PaoloEstorm/Arpmini/Arpmini_Font.h

#include <stdint.h>
#include <Arduino.h>

const uint8_t ArpminiFont[][5] PROGMEM = {
  { 0x00, 0x00, 0x00, 0x00, 0x00 },  // 0x20 32
  { 0x00, 0x5c, 0x00, 0x00, 0x00 },  // 0x21 33 !
  { 0x10, 0x28, 0x44, 0x28, 0x10 },  // 0x22 34 " = empty shift icon
  { 0x28, 0x7c, 0x28, 0x7c, 0x28 },  // 0x23 35 #
  { 0x20, 0x60, 0xfe, 0x60, 0x20 },  // 0x24 36 $ = down arrow
  { 0x44, 0x20, 0x10, 0x08, 0x44 },  // 0x25 37 %
  { 0x40, 0x40, 0x7c, 0x04, 0x04 },  // 0x26 38 & = octave icon
  { 0x60, 0x60, 0x7c, 0x0c, 0x18 },  // 0x27 39 ' = music note icon
  { 0x6c, 0x44, 0x00, 0x44, 0x6c },  // 0x28 40 ( = empty selected box
  { 0x6c, 0x7c, 0x38, 0x7c, 0x6c },  // 0x29 41 ) = full selected box
  { 0x00, 0x10, 0x28, 0x10, 0x00 },  // 0x2A 42 * = small circle
  { 0x10, 0x10, 0x7c, 0x10, 0x10 },  // 0x2B 43 +
  { 0x74, 0x68, 0x60, 0x68, 0x74 },  // 0x2C 44 , = drum icon
  { 0x10, 0x10, 0x10, 0x10, 0x10 },  // 0x2D 45 -
  { 0x00, 0x40, 0x00, 0x00, 0x00 },  // 0x2E 46 .
  { 0x00, 0x60, 0x10, 0x0c, 0x00 },  // 0x2F 47 /
  { 0x7c, 0x64, 0x54, 0x4c, 0x7c },  // 0x30 48 0
  { 0x00, 0x48, 0x7c, 0x40, 0x00 },  // 0x31 49 1
  { 0x64, 0x54, 0x54, 0x54, 0x48 },  // 0x32 50 2
  { 0x44, 0x54, 0x54, 0x54, 0x6c },  // 0x33 51 3
  { 0x3c, 0x20, 0x20, 0x70, 0x20 },  // 0x34 52 4
  { 0x5c, 0x54, 0x54, 0x54, 0x24 },  // 0x35 53 5
  { 0x7c, 0x54, 0x54, 0x54, 0x74 },  // 0x36 54 6
  { 0x04, 0x04, 0x64, 0x14, 0x0c },  // 0x37 55 7
  { 0x7c, 0x54, 0x54, 0x54, 0x7c },  // 0x38 56 8
  { 0x5c, 0x54, 0x54, 0x54, 0x7c },  // 0x39 57 9
  { 0x54, 0x50, 0x54, 0x14, 0x54 },  // 0x3A 58 : = estorm icon
  { 0xff, 0x00, 0xff, 0xff, 0x00 },  // 0x3B 59 ; = vertical lines
  { 0x00, 0x10, 0x28, 0x44, 0x00 },  // 0x3C 60 <
  { 0x28, 0x28, 0x28, 0x28, 0x28 },  // 0x3D 61 =
  { 0x00, 0x44, 0x28, 0x10, 0x00 },  // 0x3E 62 >
  { 0x08, 0x04, 0x54, 0x08, 0x00 },  // 0x3F 63 ?
  { 0x00, 0x00, 0xff, 0x00, 0x00 },  // 0x40 64 @ = vertical line
  { 0x7c, 0x14, 0x14, 0x14, 0x7c },  // 0x41 65 A
  { 0x7c, 0x54, 0x54, 0x5C, 0x70 },  // 0x42 66 B
  { 0x7c, 0x44, 0x44, 0x44, 0x44 },  // 0x43 67 C
  { 0x7c, 0x44, 0x44, 0x44, 0x38 },  // 0x44 68 D
  { 0x7c, 0x54, 0x54, 0x54, 0x44 },  // 0x45 69 E
  { 0x7c, 0x14, 0x14, 0x14, 0x04 },  // 0x46 70 F
  { 0x7c, 0x44, 0x54, 0x54, 0x74 },  // 0x47 71 G
  { 0x7c, 0x10, 0x10, 0x10, 0x7c },  // 0x48 72 H
  { 0x44, 0x44, 0x7c, 0x44, 0x44 },  // 0x49 73 I
  { 0x60, 0x44, 0x44, 0x7c, 0x04 },  // 0x4A 74 J
  { 0x7c, 0x10, 0x10, 0x28, 0x44 },  // 0x4B 75 K
  { 0x7c, 0x40, 0x40, 0x40, 0x40 },  // 0x4C 76 L
  { 0x7c, 0x08, 0x10, 0x08, 0x7c },  // 0x4D 77 M
  { 0x7c, 0x08, 0x10, 0x20, 0x7c },  // 0x4E 78 N
  { 0x38, 0x44, 0x44, 0x44, 0x38 },  // 0x4F 79 O
  { 0x7c, 0x14, 0x14, 0x14, 0x1C },  // 0x50 80 P
  { 0x3c, 0x24, 0x64, 0x24, 0x3c },  // 0x51 81 Q
  { 0x7c, 0x14, 0x14, 0x34, 0x5C },  // 0x52 82 R
  { 0x5c, 0x54, 0x54, 0x54, 0x74 },  // 0x53 83 S
  { 0x04, 0x04, 0x7c, 0x04, 0x04 },  // 0x54 84 T
  { 0x7c, 0x40, 0x40, 0x40, 0x7c },  // 0x55 85 U
  { 0x0c, 0x30, 0x40, 0x30, 0x0c },  // 0x56 86 V
  { 0x3c, 0x40, 0x30, 0x40, 0x3c },  // 0x57 87 W
  { 0x44, 0x28, 0x10, 0x28, 0x44 },  // 0x58 88 X
  { 0x0c, 0x10, 0x60, 0x10, 0x0c },  // 0x59 89 Y
  { 0x44, 0x64, 0x54, 0x4c, 0x44 },  // 0x5A 90 Z
  { 0x7c, 0x44, 0x44, 0x44, 0x7c },  // 0x5B 91 [ = empty box
  { 0x10, 0x10, 0x00, 0x08, 0x7c },  // 0x5C 92 "\" = "-1" icon
  { 0x7c, 0x7c, 0x7c, 0x7c, 0x7c },  // 0x5D 93 ] = full box
  { 0x20, 0x10, 0x08, 0x10, 0x20 },  // 0x5E 94 ^ = up cursor
  { 0x08, 0x10, 0x20, 0x10, 0x08 },  // 0x5F 95 _ = down cursor
  { 0x10, 0x28, 0xc7, 0x00, 0x00 },  // 0x60 96 ` = vertical line with triangle
  { 0x10, 0x38, 0x7c, 0x38, 0x10 },  // 0x61 97 a = full shift icon
};
